e-tinkers/ATtiny3217_Li-Ion_LiPo_battery_capacity_tester/hardware/battery_capacity_tester.kicad_sch

## KiCad design hardware/battery_capacity_tester.kicad_sch (2026-02-04)

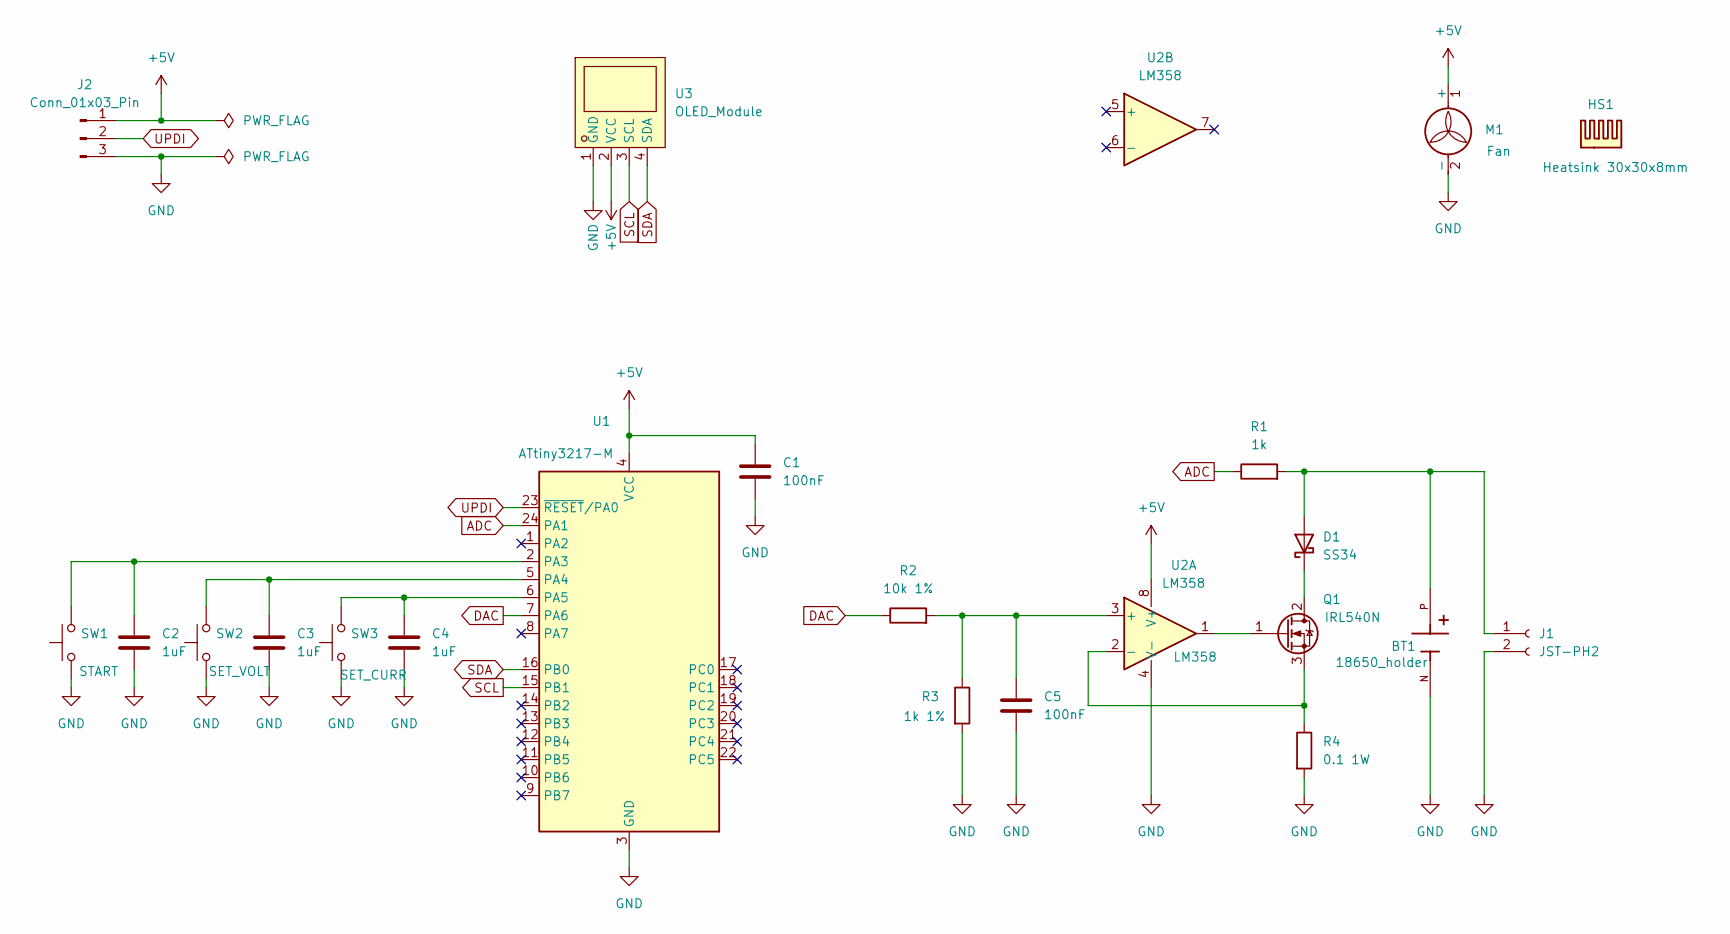
[picture p3: schematic battery_capacity_tester.kicad_sch]

Parts:
BT1: 18650_holder; BAT-SMD_MY-18650-02
C1, C5: 100nF
C2, C3, C4: 1uF
D1: SS34; D_SMA
HS1: Heatsink 30x30x8mm
J1: JST-PH2
J2: Conn_01x03_Pin
M1: Fan
Q1: IRL540N; TO-220-3_Vertical
R1: 1k
R2: 10k 1%
R3: 1k 1%
R4: 0.1 1W
SW1: START
SW2: SET_VOLT
SW3: SET_CURR
U1: ATtiny3217-M; QFN-24-1EP_4x4mm_P0.5mm_EP2.6x2.6mm
U2: LM358
U3: OLED_Module; OLED-0.66_L23.44-W19-P2.54

Connections:
+5V: C1.1, J2.1, M1.1 (+), U1.4 (VCC), U2.8 (V+), U3.2 (VCC)
ADC: R1.1, U1.24 (PA1)
DAC: R2.1, U1.7 (PA6)
GND: BT1.N, C1.2, C2.2, C3.2, C4.2, C5.2, J1.2, J2.3, M1.2 (-), R3.2, R4.2, SW1.1, SW2.1, SW3.1, U1.3 (GND), U1.25 (GND), U2.4 (V-), U3.1 (GND)
unnamed: BT1.P, D1.2 (A), J1.1, R1.2
unnamed: C2.1, SW1.2, U1.2 (PA3)
unnamed: C3.1, SW2.2, U1.5 (PA4)
unnamed: C4.1, SW3.2, U1.6 (PA5)
unnamed: C5.1, R2.2, R3.1, U2.3 (+)
unnamed: D1.1 (K), Q1.2 (D)
unnamed: Q1.1 (G), U2.1
unnamed: Q1.3 (S), R4.1, U2.2 (-)
SCL: U1.15 (PB1), U3.3 (SCL)
SDA: U1.16 (PB0), U3.4 (SDA)
UPDI: J2.2, U1.23 (~RESET/PA0)
